MartinNOsores/Proyecto-CISAR/Programación/Pruebas db bot telegram/Api_activador_de_URL.py

#print("¿Elija numero 1 o numero 2?")

#if(input()==s):
#  print("la opcion elegida es", nombre)

import requests
import time
n = 1

while n>0:

  r = requests.get("https://api.telegram.org/bot1611398547:AAEOgMyfYm-5U1j03oqvFtg-I7GVpN7d9Eg/sendMessage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")
  with open("index.html", "wb") as f:
    f.write(r.content)
    r.close()
  time.sleep(10)
